iikochma/taco-keyboard/images/case-render-bottom.PNG

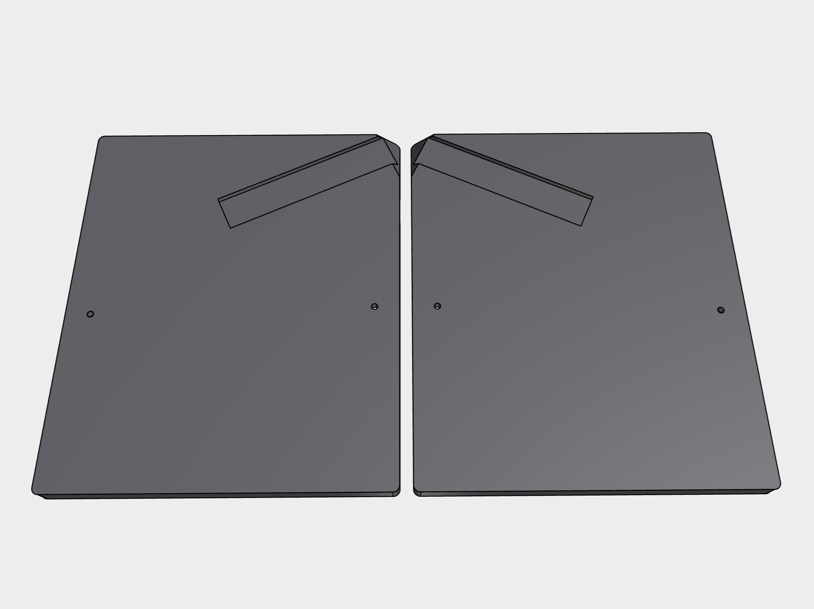
images/case-render-bottom.PNG
