iikochma/taco-keyboard/images/keyboard-front-view.jpg

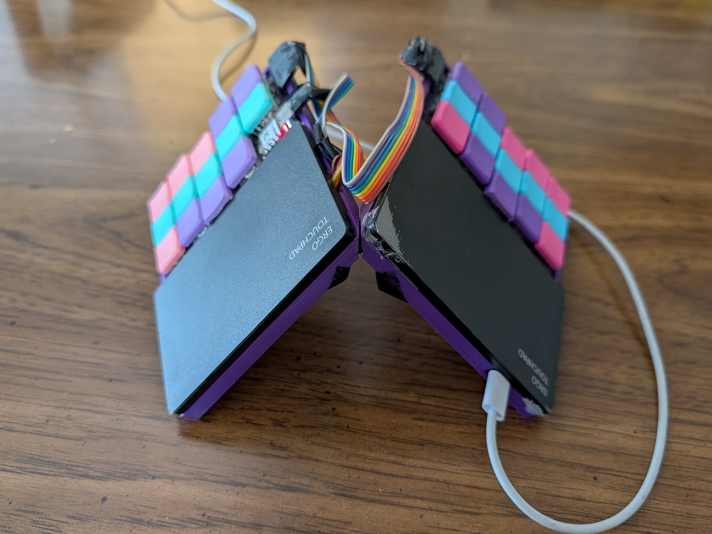
images/keyboard-front-view.jpg
