iikochma/taco-keyboard/images/keyboard-right-hand.jpg

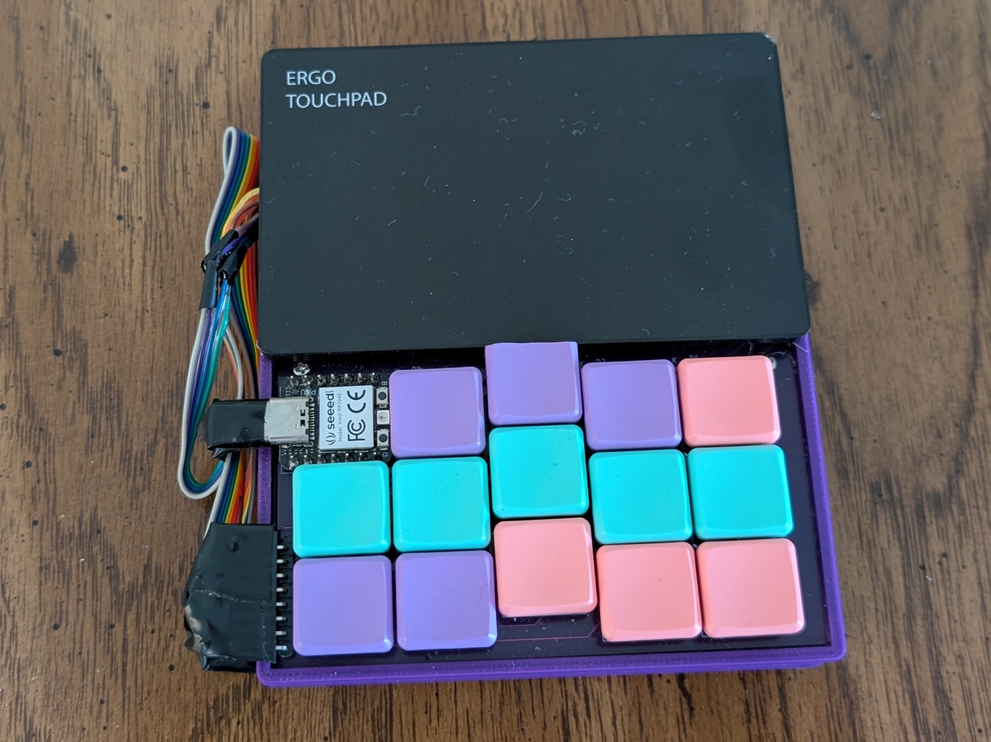
images/keyboard-right-hand.jpg
