iikochma/taco-keyboard/images/pcb-left-side.jpg

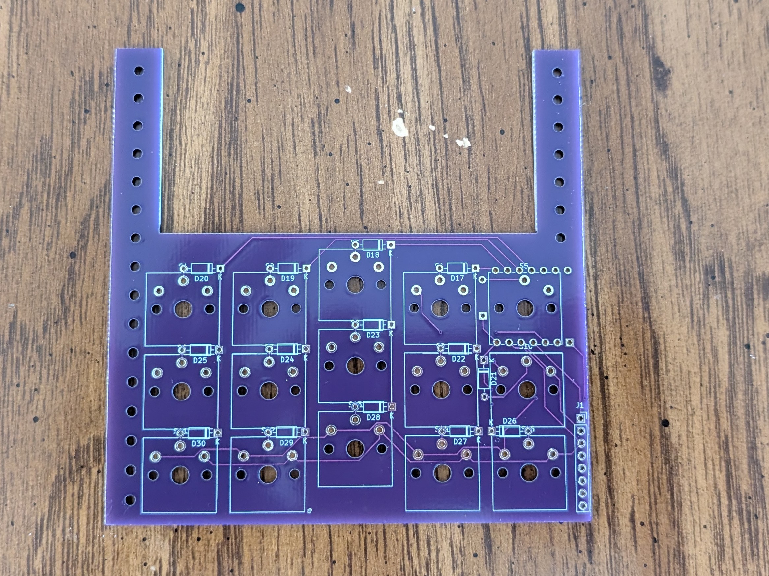
images/pcb-left-side.jpg
